prgazevedo/PWDTracker/_GPSUtils.h

/*
 * Copyright 2018 Pedro Azevedo (prgazevedo@gmail.com)
 * and other contributors as indicated by the @author tags.
 **********************************************************************
 * Licensed under the Apache License, Version 2.0 (the "License");
 * you may not use this file except in compliance with the License.
 * You may obtain a copy of the License at
 *
 *    http://www.apache.org/licenses/LICENSE-2.0
 *
 * Unless required by applicable law or agreed to in writing, software
 * distributed under the License is distributed on an "AS IS" BASIS,
 * WITHOUT WARRANTIES OR CONDITIONS OF ANY KIND, either express or implied.
 * See the License for the specific language governing permissions and
 * limitations under the License.
 */
#include <TinyGPS++.h>

// The TinyGPS++ object
TinyGPSPlus gps;

 
// This custom version of delay() ensures that the gps object
// is being "fed".
static void smartDelay(unsigned long ms)
{
  unsigned long start = millis();
  do 
  {
    while (Serial2.available())
      gps.encode(Serial2.read());
  } while (millis() - start < ms);
}


static void printFloat(float val, bool valid, int len, int prec)
{
  if (!valid)
  {
    while (len-- > 1)
      Serial.print('*');
    Serial.print(' ');
  }
  else
  {
    Serial.print(val, prec);
    int vi = abs((int)val);
    int flen = prec + (val < 0.0 ? 2 : 1); // . and -
    flen += vi >= 1000 ? 4 : vi >= 100 ? 3 : vi >= 10 ? 2 : 1;
    for (int i=flen; i<len; ++i)
      Serial.print(' ');
  }
  smartDelay(0);
}

static void printInt(unsigned long val, bool valid, int len)
{
  char sz[32] = "*****************";
  if (valid)
    sprintf(sz, "%ld", val);
  sz[len] = 0;
  for (int i=strlen(sz); i<len; ++i)
    sz[i] = ' ';
  if (len > 0) 
    sz[len-1] = ' ';
  Serial.print(sz);
  smartDelay(0);
}

static void printDateTime(TinyGPSDate &d, TinyGPSTime &t)
{
  if (!d.isValid())
  {
    Serial.print(F("********** "));
  }
  else
  {
    char sz[32];
    sprintf(sz, "%02d/%02d/%02d ", d.month(), d.day(), d.year());
    Serial.print(sz);
  }
  
  if (!t.isValid())
  {
    Serial.print(F("******** "));
  }
  else
  {
    char sz[32];
    sprintf(sz, "%02d:%02d:%02d ", t.hour(), t.minute(), t.second());
    Serial.print(sz);
  }

  printInt(d.age(), d.isValid(), 5);
  smartDelay(0);
}

static void printStr(const char *str, int len)
{
  int slen = strlen(str);
  for (int i=0; i<len; ++i)
    Serial.print(i<slen ? str[i] : ' ');
  smartDelay(0);
}

char nibble2c(char c)
{
   if ((c>='0') && (c<='9'))
      return c-'0' ;
   if ((c>='A') && (c<='F'))
      return c+10-'A' ;
   if ((c>='a') && (c<='a'))
      return c+10-'a' ;
   return -1 ;
}

char hex2c(char c1, char c2)
{
   if(nibble2c(c2) >= 0)
     return nibble2c(c1)*16+nibble2c(c2) ;
   return nibble2c(c1) ;
}

String hex2str(char *data)
{
   String result = "" ;
   for (int i=0 ; nibble2c(data[i])>=0 ; i++)
   {
      result += hex2c(data[i],data[i+1]) ;
      if(nibble2c(data[i+1])>=0)
        i++ ;
   }
   return result;
}
